winnedatsch/aW_1-keyboard/case/right/layer3.dxf

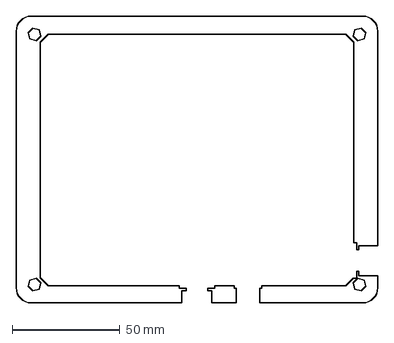
[picture p19: CAD file, 2020-08-14]
case/right/layer3.dxf
167.4 x 132.8 mm
