winnedatsch/aW_1-keyboard/case/left/left_layer1.dxf

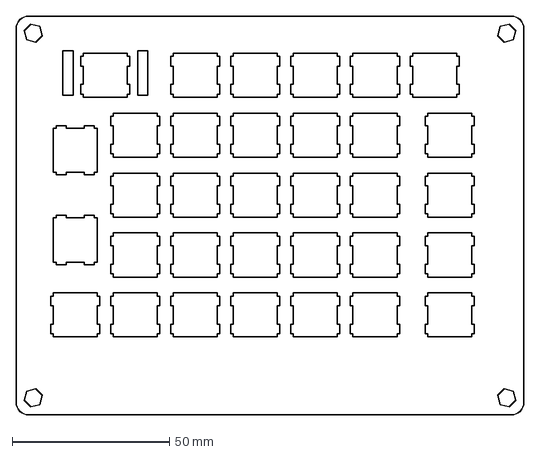
[picture p20: CAD file, 2020-08-14]
case/left/left_layer1.dxf
161.4 x 126.8 mm
