winnedatsch/aW_1-keyboard/case/right/layer5.dxf

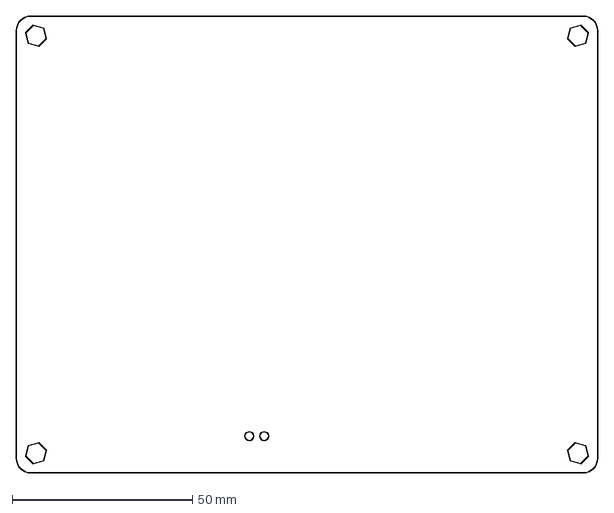
[picture p21: CAD file, 2020-08-14]
case/right/layer5.dxf
161.4 x 126.8 mm
