winnedatsch/aW_1-keyboard/firmware/custom/src/battery_reader.cpp

/*
 Battery.cpp - Battery library
 Copyright (c) 2014 Roberto Lo Giacco.

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
 You should have received a copy of the GNU General Public License
 along with this program.  If not, see <http://www.gnu.org/licenses/>.
 */

#include "battery_reader.h"
#include <logging/log.h>
LOG_MODULE_REGISTER(battery_reader);


BatteryReader::BatteryReader(std::shared_ptr<device> adc_device, uint16_t ref_voltage,
                             uint16_t min_voltage, uint16_t max_voltage, uint8_t sense_pin,
                             float divider_ratio, const map_fn map_function)
    : adc_device{adc_device},
      ref_voltage{ref_voltage},
      min_voltage{min_voltage},
      max_voltage{max_voltage},
      divider_ratio{divider_ratio},
      map_function{map_function},
      channel_config{.gain = ADC_GAIN_1_6,
                     .reference = ADC_REF_INTERNAL,
                     .acquisition_time = ADC_ACQ_TIME_DEFAULT,
                     .channel_id = sense_pin,
                     .differential = 0,
                     .input_positive = (uint8_t)(sense_pin + 1)} {
    int error = adc_channel_setup(adc_device.get(), &channel_config);
    if (error) {
        LOG_ERR("ADC setup failed");
    } else {
        LOG_INF("ADC setup succeeded");
    }
}

uint8_t BatteryReader::level() { return this->level(this->voltage()); }

uint8_t BatteryReader::level(uint16_t voltage) {
    if (voltage <= min_voltage) {
        return 0;
    } else if (voltage >= max_voltage) {
        return 100;
    } else {
        return map_function(voltage, min_voltage, max_voltage);
    }
}

uint16_t BatteryReader::voltage() {
    const adc_sequence sequence = {
        .options = NULL,                                   // extra samples and callback
        .channels = BIT(this->channel_config.channel_id),  // bit mask of channels to read
        .buffer = &(this->sample_buffer),                  // where to put samples read
        .buffer_size = sizeof(this->sample_buffer),
        .resolution = 10,   // desired resolution
        .oversampling = 0,  // don't oversample
        .calibrate = 0      // don't calibrate
    };

    int error = adc_read(adc_device.get(), &sequence);

    if (error) {
        LOG_ERR("ADC sampling failed");
        return 0;
    } else {
        uint16_t reading = this->sample_buffer * divider_ratio * ref_voltage / 1024;
        LOG_INF("Battery reading: %umV", reading);
        return reading;
    }
}
